vanyap1/XMEGA256A3BU_SmartHome_Gateway/XMEGA_A3BU/config.h

/*
 * config.h
 *
 * Created: 02.01.2025 15:56:56
 *  Author: Ivan Prints
 */ 

#ifndef SYS_CONFIG_H
#define SYS_CONFIG_H

// <<< Use Configuration Wizard in Context Menu >>>

#ifndef F_CPU
#define F_CPU 32000000UL
#endif

#ifndef DEB_SERIAL_BAUD
#define DEB_SERIAL_BAUD 115200UL
#endif

// <<< end of configuration section >>>

#endif // CLOCK_CONFIG_H
